JUNIORLARA24/folded-dipole-array-5GHz/results/dipolo_rad.png

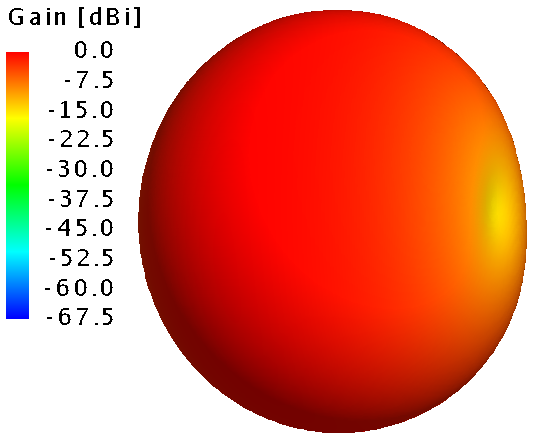
results/dipolo_rad.png
