JUNIORLARA24/folded-dipole-array-5GHz/results/4x4.png

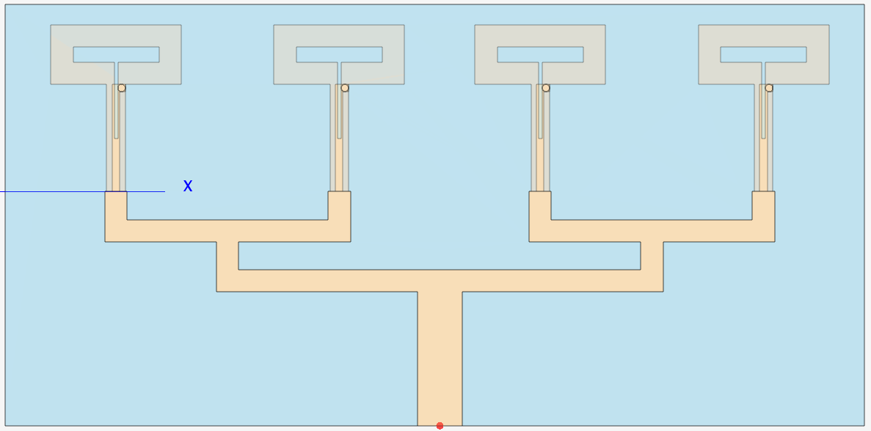
results/4x4.png
