JUNIORLARA24/folded-dipole-array-5GHz/results/arreglo_3d.jpg

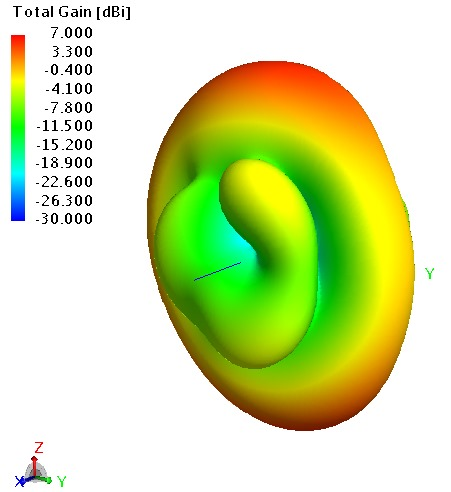
results/arreglo_3d.jpg
