JUNIORLARA24/folded-dipole-array-5GHz/results/arreglo_carta.png

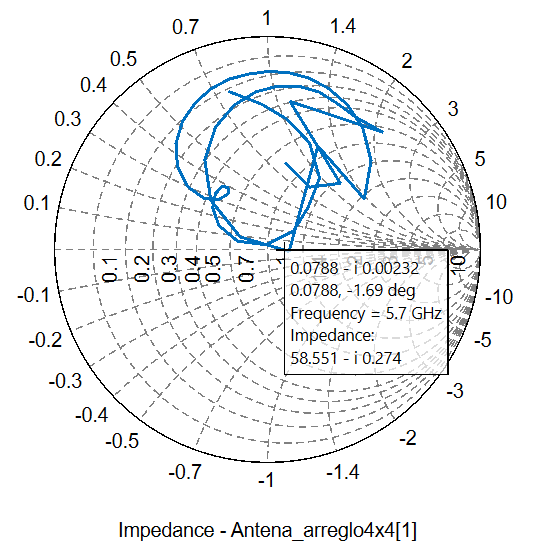
results/arreglo_carta.png
