JUNIORLARA24/folded-dipole-array-5GHz/results/arreglo_phi.png

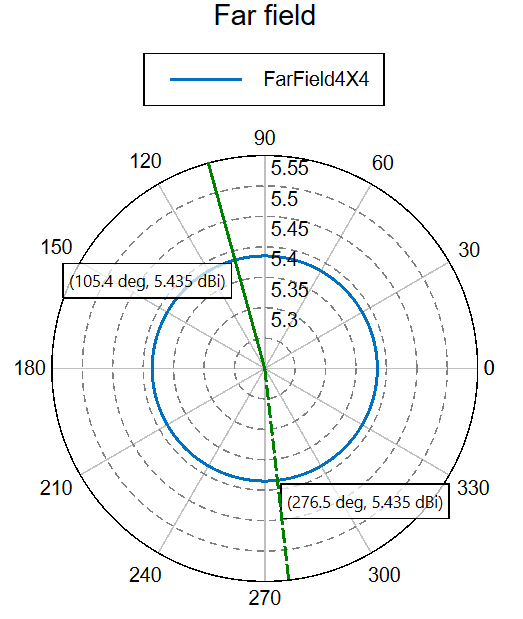
results/arreglo_phi.png
