JUNIORLARA24/folded-dipole-array-5GHz/results/arreglo_s11.png

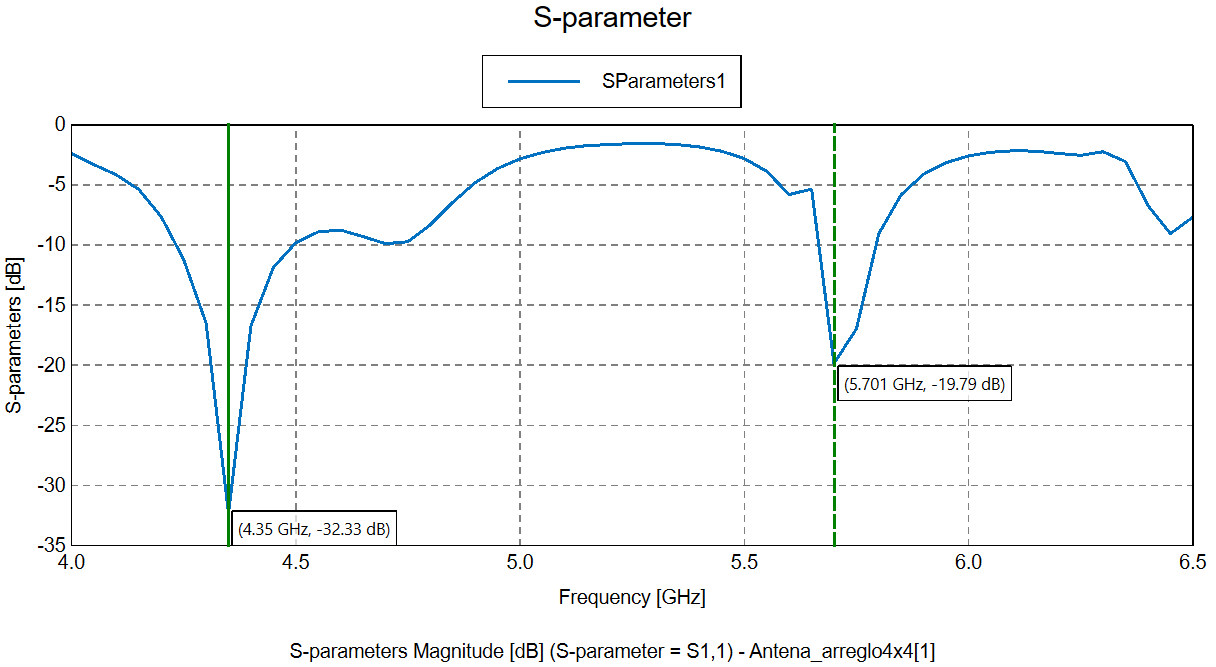
results/arreglo_s11.png
