JUNIORLARA24/folded-dipole-array-5GHz/results/arreglo_theta.png

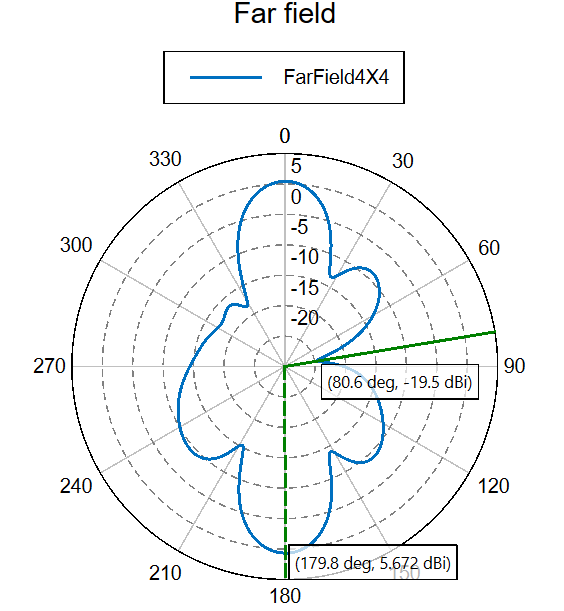
results/arreglo_theta.png
