JUNIORLARA24/folded-dipole-array-5GHz/results/dip_down.png

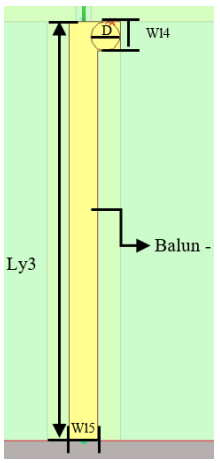
results/dip_down.png
