JUNIORLARA24/folded-dipole-array-5GHz/results/dip_feko.png

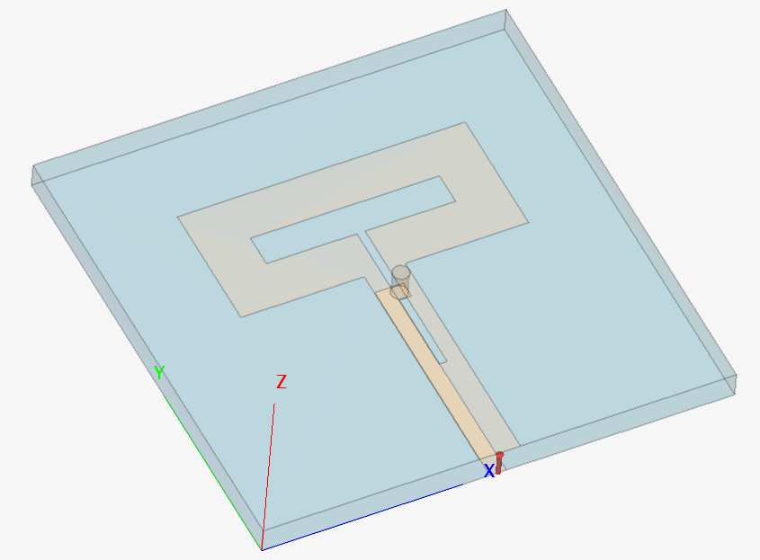
results/dip_feko.png
