JUNIORLARA24/folded-dipole-array-5GHz/results/dip_top.png

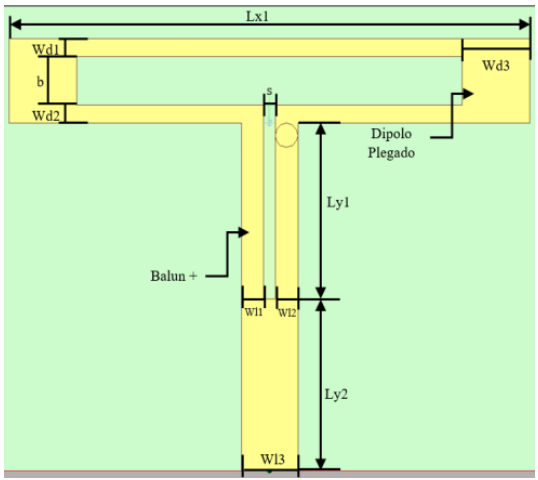
results/dip_top.png
