JUNIORLARA24/folded-dipole-array-5GHz/results/dipolo_carta.png

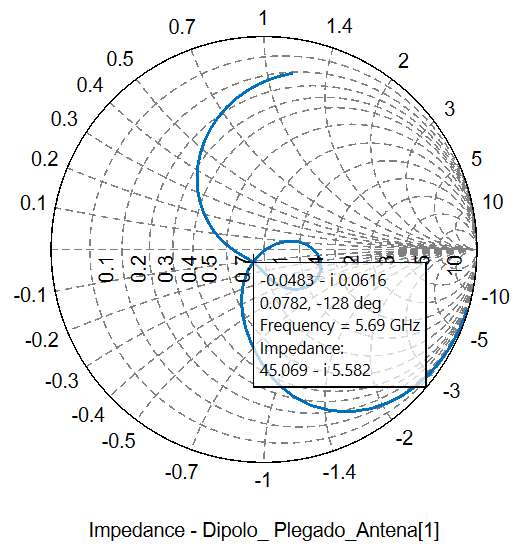
results/dipolo_carta.png
