JUNIORLARA24/folded-dipole-array-5GHz/results/dipolo_elev.png

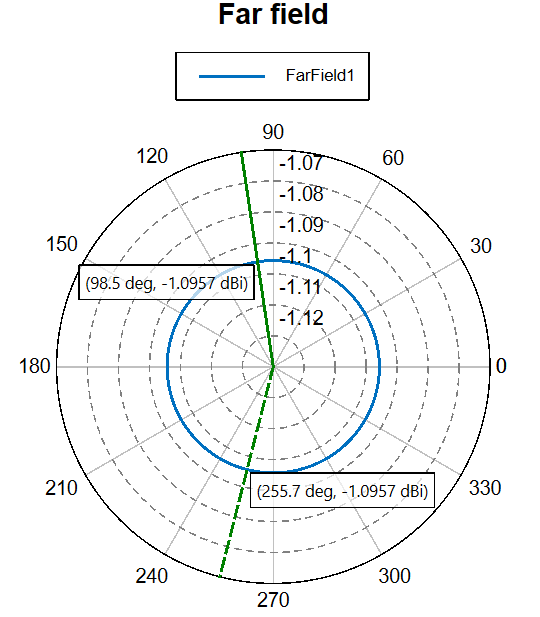
results/dipolo_elev.png
