JUNIORLARA24/folded-dipole-array-5GHz/results/dipolo_s11.png

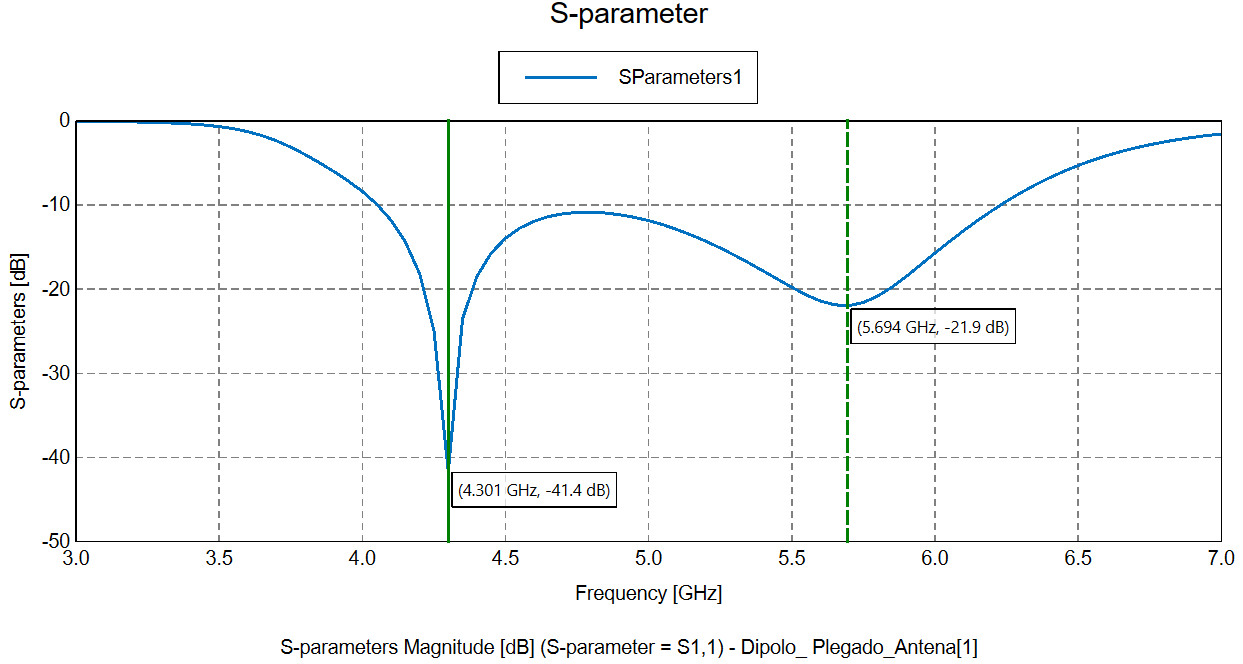
results/dipolo_s11.png
