JUNIORLARA24/folded-dipole-array-5GHz/results/dipolo_thet.png

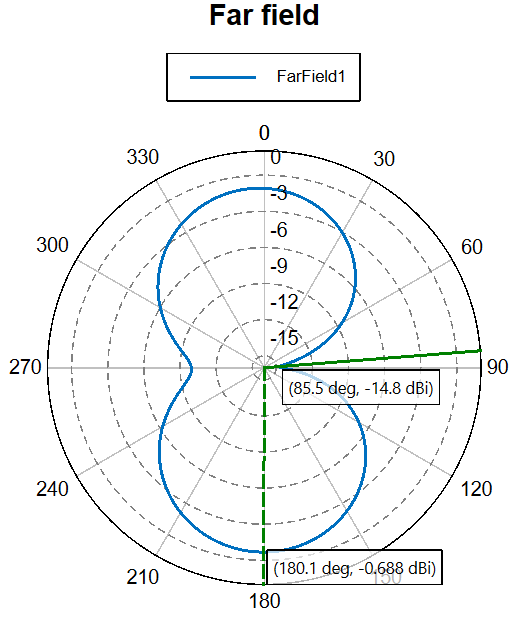
results/dipolo_thet.png
