JUNIORLARA24/folded-dipole-array-5GHz/results/s11_comp.png

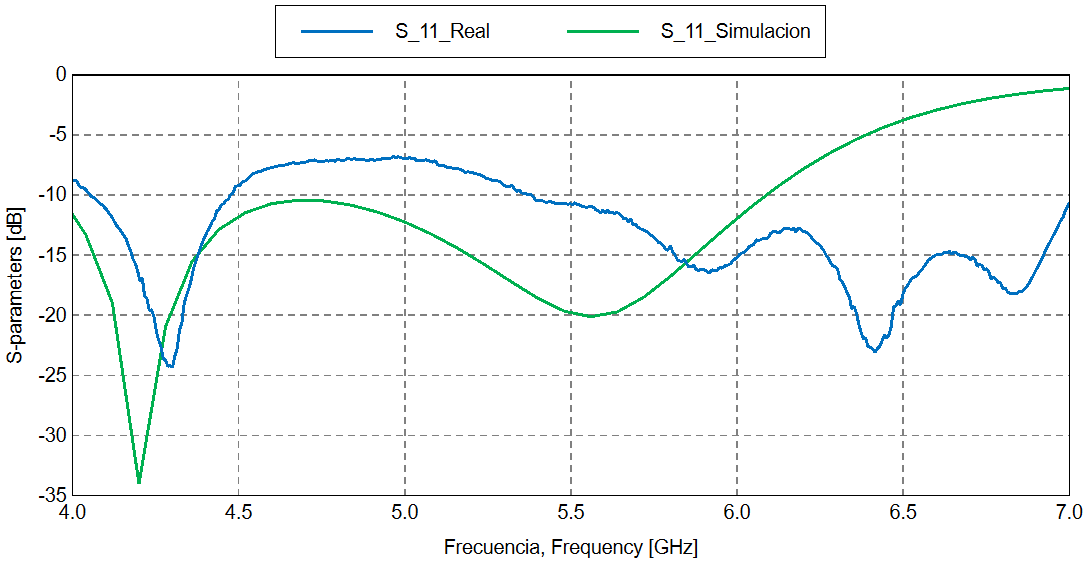
results/s11_comp.png
