JUNIORLARA24/folded-dipole-array-5GHz/results/s11_real.png

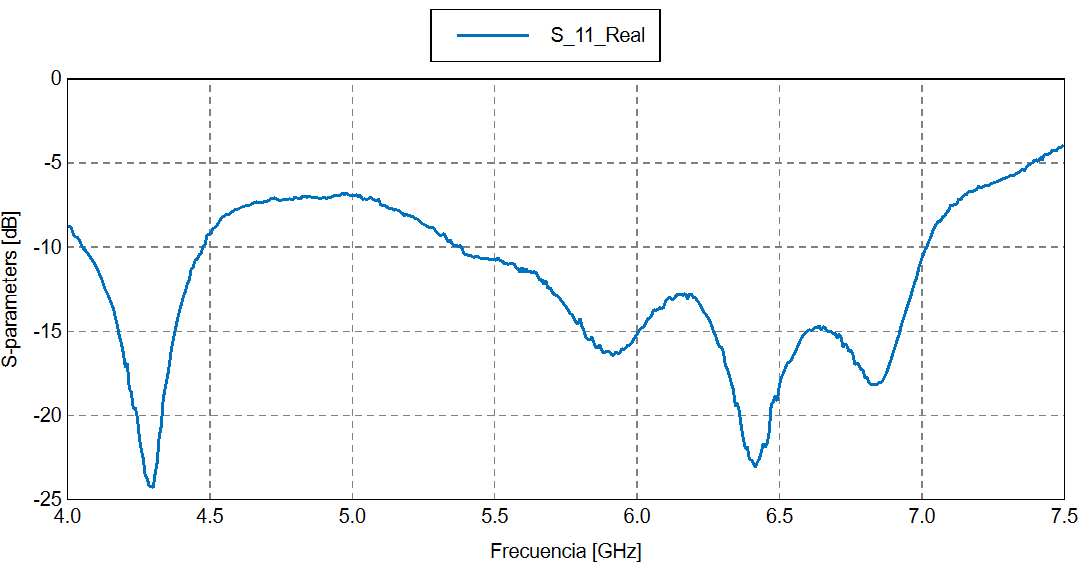
results/s11_real.png
